commonkestrel/physical-digital-darts/python/SimulateDartboard.py

import serial.tools.list_ports
import time, math
from DartboardSimulator import DartboardSimulator

useSerial = True

if useSerial:
    ports = serial.tools.list_ports.comports()
    serialInst = serial.Serial('COM5', 115200)
    time.sleep(0.5)
    print("Serial Connected!")

#event roll pitch yaw velocity

#0 angle angle angle speed
#0 - not pressed
#1 - if pressed
#2 - just pressed
#3 - just released

dartboardSimulator = DartboardSimulator(3)
max_parsed_speed = 0.35
desired_parsed_speed = 150

def throttle_curve(throttle):
    return desired_parsed_speed*math.tanh(3*throttle/max_parsed_speed)

while dartboardSimulator.loop(should_throw_debug=True, should_preview_debug=False):
    if useSerial:
        try:
            data = serialInst.readline().decode('utf-8').strip()
        except serial.SerialException:
            print("Serial monitor disconnected")
            continue
        
        try:
            parsedData = list(map(float, data.strip().split()))
            #print(parsedData)
        except ValueError:
            print(f'parsedData ({data}) is not a list of floats separated by spaces')
            continue
        
        if parsedData:
            parsedButtonState = parsedData[0]
            parsedRoll, parsedPitch, parsedYaw = parsedData[1], parsedData[2], parsedData[3] 
            parsedSpeed = parsedData[4] 
            
            #print(f'Angles before time of throw: Yaw: {parsedYaw}, Pitch: {parsedPitch}, Speed:{parsedSpeed}')

            dart_should_be_thrown = parsedButtonState == 3
            if dart_should_be_thrown:
                #parsedSpeed = throttle_curve(parsedSpeed)
                parsedSpeed=desired_parsed_speed
                #print(f"Adjusted parsedSpeed {parsedSpeed}")
                depth = 1*math.cos(math.radians(parsedYaw))*math.sin(math.radians(parsedPitch))
                left_and_right_movement = math.sin(math.radians(parsedYaw))*math.sin(math.radians(parsedPitch))*parsedSpeed
                up_and_down_movement = math.cos(math.radians(parsedPitch))*parsedSpeed
                dartboardSimulator.throw_dart([left_and_right_movement, up_and_down_movement, depth])

#serialInst.close()
print("This actually happened!")
